Tinkerforge/solid-state-relay-v2-bricklet/software/src/communication.c

/* solid-state-relay-v2-bricklet
 * Copyright (C) 2017 Olaf Lüke <olaf@tinkerforge.com>
 *
 * communication.c: TFP protocol message handling
 *
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
 * You should have received a copy of the GNU Lesser General Public
 * License along with this library; if not, write to the
 * Free Software Foundation, Inc., 59 Temple Place - Suite 330,
 * Boston, MA 02111-1307, USA.
 */

#include "communication.h"

#include "bricklib2/utility/communication_callback.h"
#include "bricklib2/protocols/tfp/tfp.h"
#include "bricklib2/hal/system_timer/system_timer.h"

#include "relay.h"

extern Relay relay;

BootloaderHandleMessageResponse handle_message(const void *message, void *response) {
	switch(tfp_get_fid_from_message(message)) {
		case FID_SET_STATE: return set_state(message);
		case FID_GET_STATE: return get_state(message, response);
		case FID_SET_MONOFLOP: return set_monoflop(message);
		case FID_GET_MONOFLOP: return get_monoflop(message, response);
		default: return HANDLE_MESSAGE_RESPONSE_NOT_SUPPORTED;
	}
}


BootloaderHandleMessageResponse set_state(const SetState *data) {
	relay.state_new = true;
	relay.state = data->state;

	return HANDLE_MESSAGE_RESPONSE_EMPTY;
}

BootloaderHandleMessageResponse get_state(const GetState *data, GetState_Response *response) {
	response->header.length = sizeof(GetState_Response);
	response->state = relay.state;

	return HANDLE_MESSAGE_RESPONSE_NEW_MESSAGE;
}

BootloaderHandleMessageResponse set_monoflop(const SetMonoflop *data) {
	relay.monoflop_new = true;
	relay.monoflop_state = data->state;
	relay.monoflop_time = data->time;
	relay.monoflop_time_remaining = data->time;

	return HANDLE_MESSAGE_RESPONSE_EMPTY;
}

BootloaderHandleMessageResponse get_monoflop(const GetMonoflop *data, GetMonoflop_Response *response) {
	response->header.length = sizeof(GetMonoflop_Response);
	response->state = relay.state;
	response->time = relay.monoflop_time;
	response->time_remaining = relay.monoflop_time_remaining;

	return HANDLE_MESSAGE_RESPONSE_NEW_MESSAGE;
}

bool handle_monoflop_done_callback(void) {
	static bool is_buffered = false;
	static MonoflopDone_Callback cb;

	if(!is_buffered) {
		if(relay.monoflop_done) {
			tfp_make_default_header(&cb.header, bootloader_get_uid(), sizeof(MonoflopDone_Callback), FID_CALLBACK_MONOFLOP_DONE);
			cb.state = relay.state;

			relay.monoflop_done = false;
		} else {
			return false;
		}
	}

	if(bootloader_spitfp_is_send_possible(&bootloader_status.st)) {
		bootloader_spitfp_send_ack_and_message(&bootloader_status, (uint8_t*)&cb, sizeof(MonoflopDone_Callback));
		is_buffered = false;
		return true;
	} else {
		is_buffered = true;
	}

	return false;
}

void communication_tick(void) {
	communication_callback_tick();
}

void communication_init(void) {
	communication_callback_init();
}
